LCQIANN/esp32s3-camera/enclosure/esp32s3-camera-shell-front.png

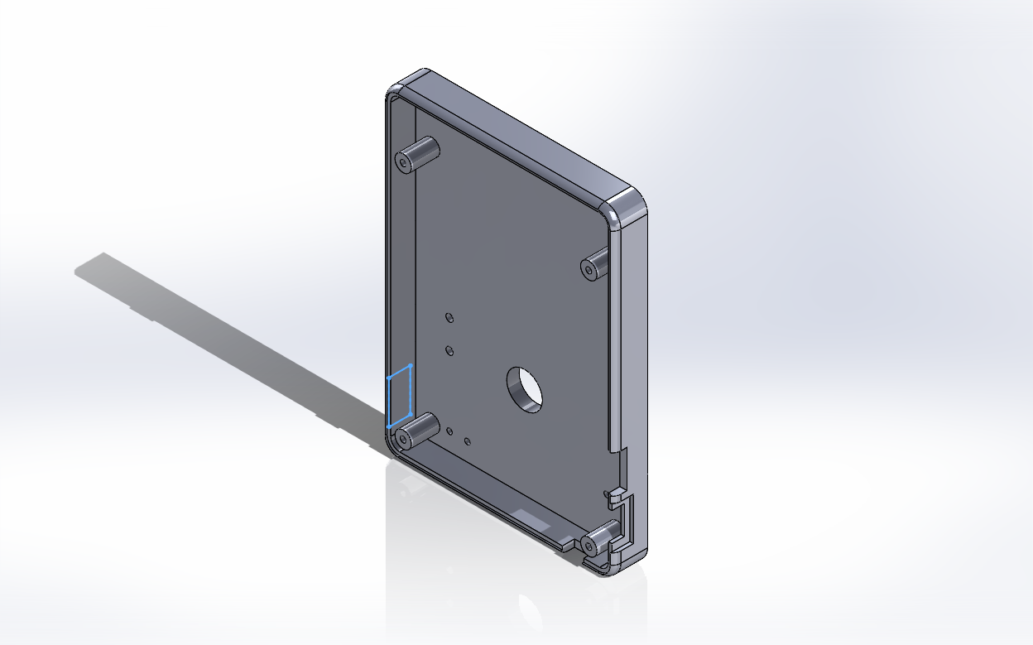
enclosure/esp32s3-camera-shell-front.png
