LCQIANN/esp32s3-camera/enclosure/esp32s3-camera-shutter-cap.png

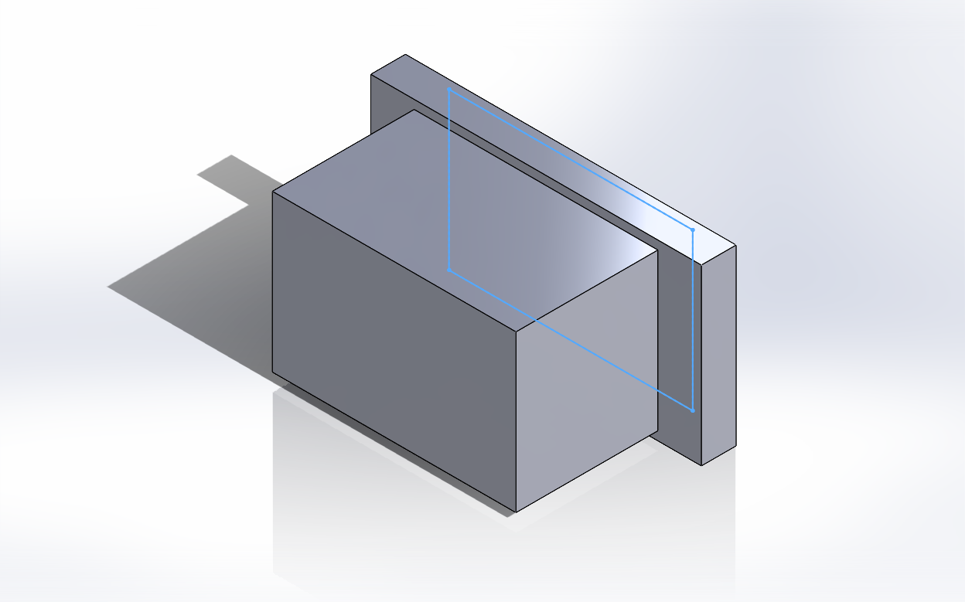
enclosure/esp32s3-camera-shutter-cap.png
