LCQIANN/esp32s3-camera/enclosure/fit-back-open-flat.png

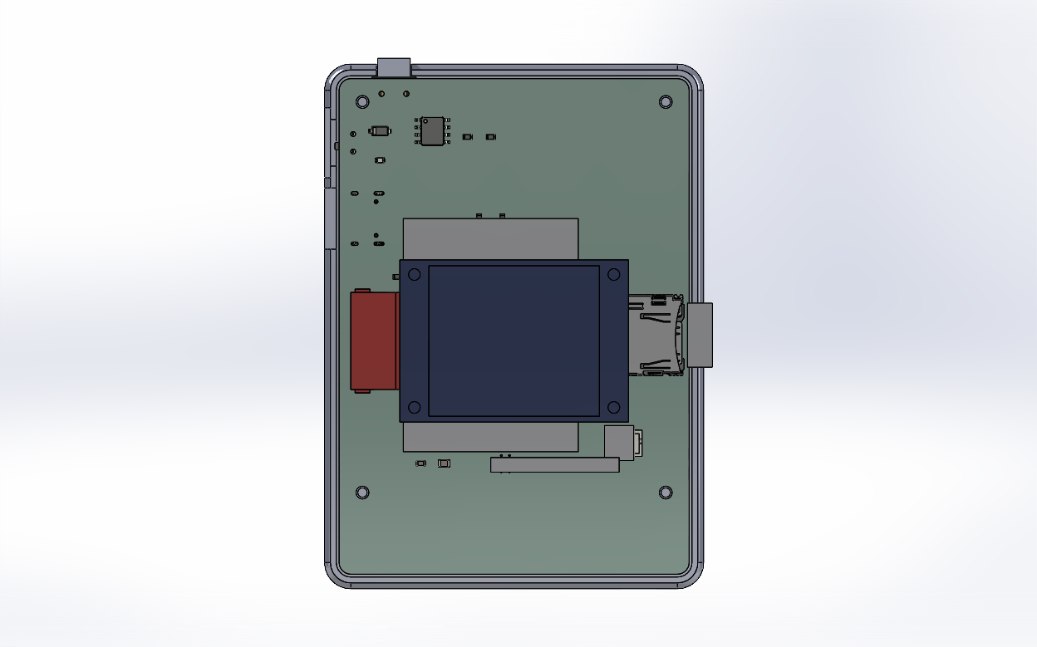
enclosure/fit-back-open-flat.png
