LCQIANN/esp32s3-camera/enclosure/fit-front-open-top.png

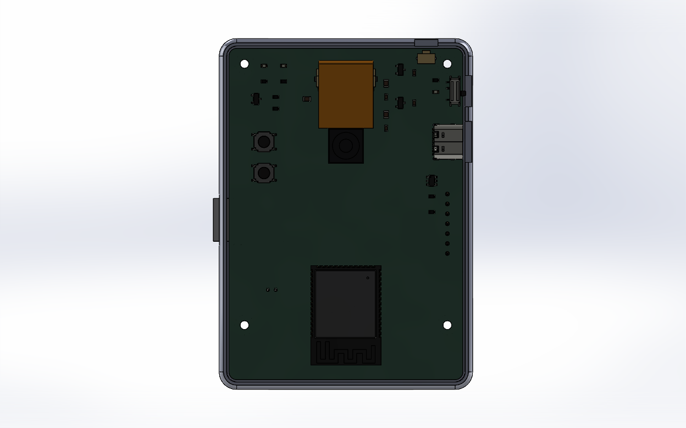
enclosure/fit-front-open-top.png
