LCQIANN/esp32s3-camera/enclosure/offboard-battery-card.png

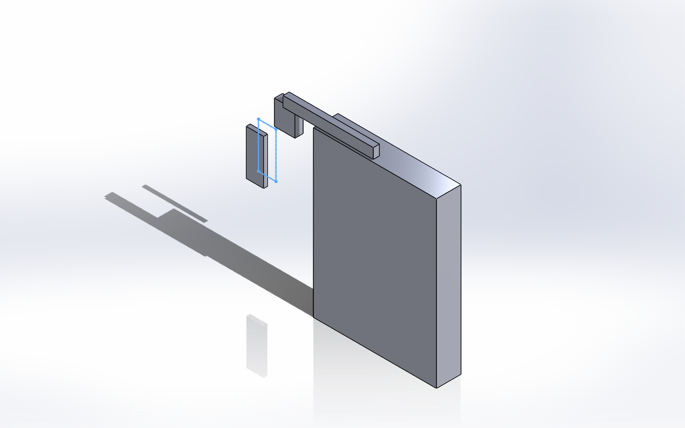
enclosure/offboard-battery-card.png
