LCQIANN/esp32s3-camera/enclosure/offboard-camera-module.png

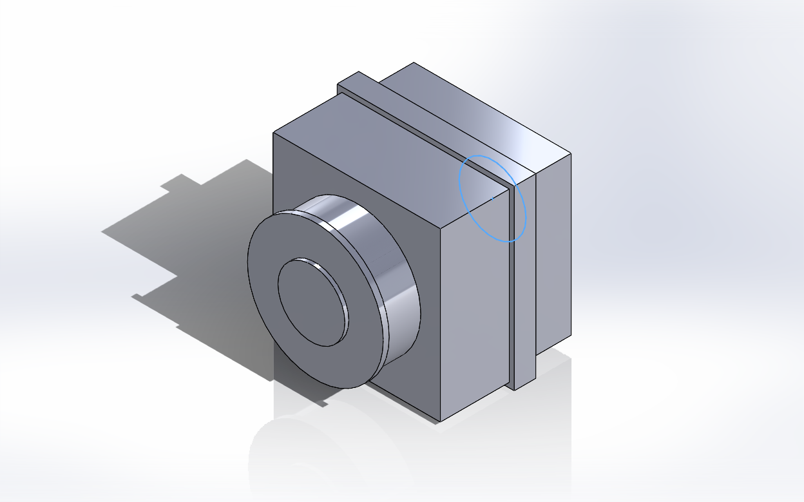
enclosure/offboard-camera-module.png
