LCQIANN/esp32s3-camera/enclosure/offboard-display-cable.png

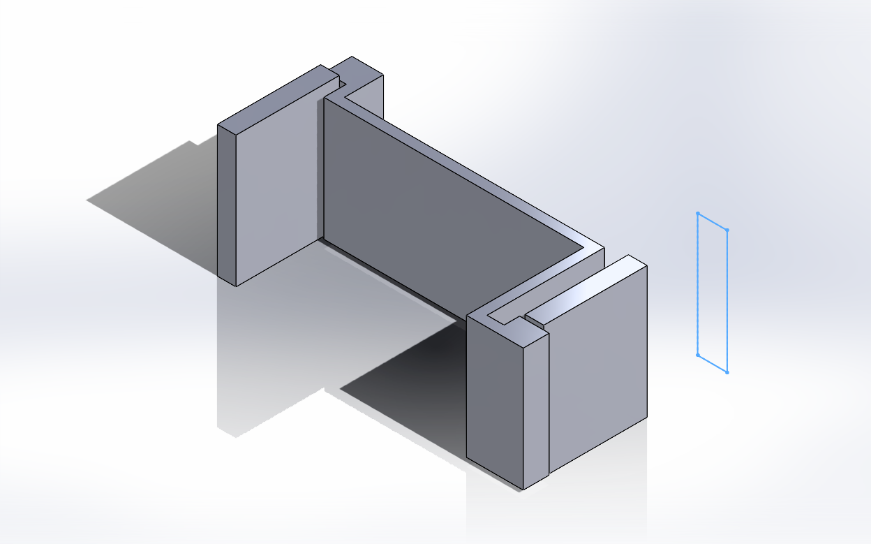
enclosure/offboard-display-cable.png
