LCQIANN/esp32s3-camera/enclosure/offboard-display-module.png

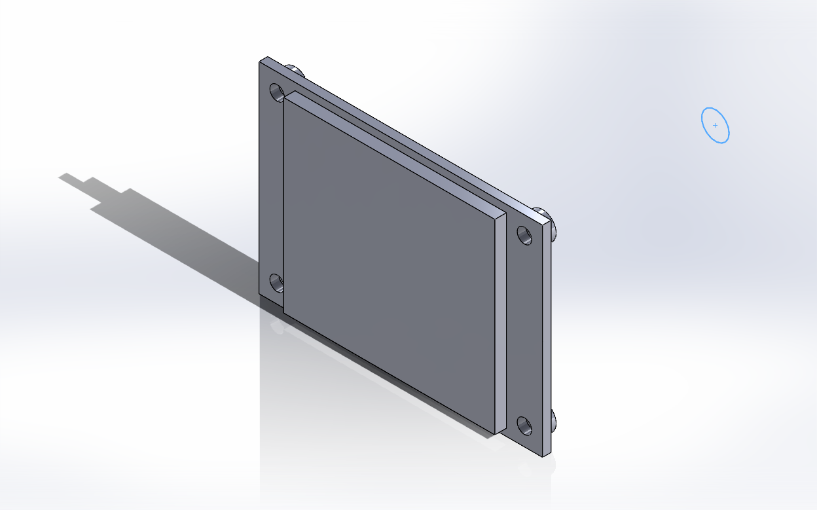
enclosure/offboard-display-module.png
