LCQIANN/esp32s3-camera/frames/s00.jpg

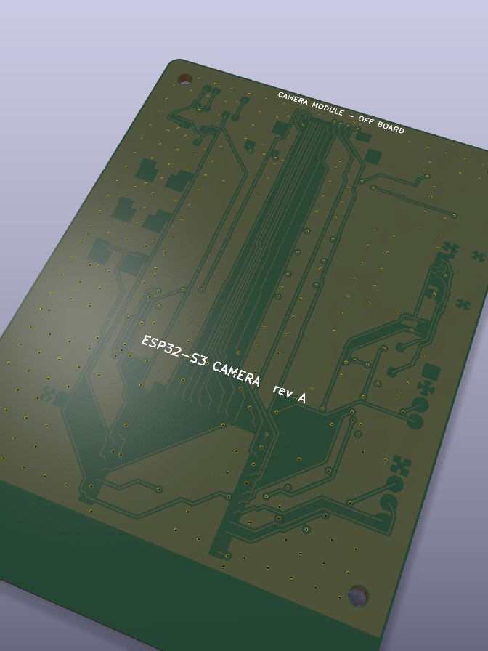
frames/s00.jpg
