LCQIANN/esp32s3-camera/frames/s01.jpg

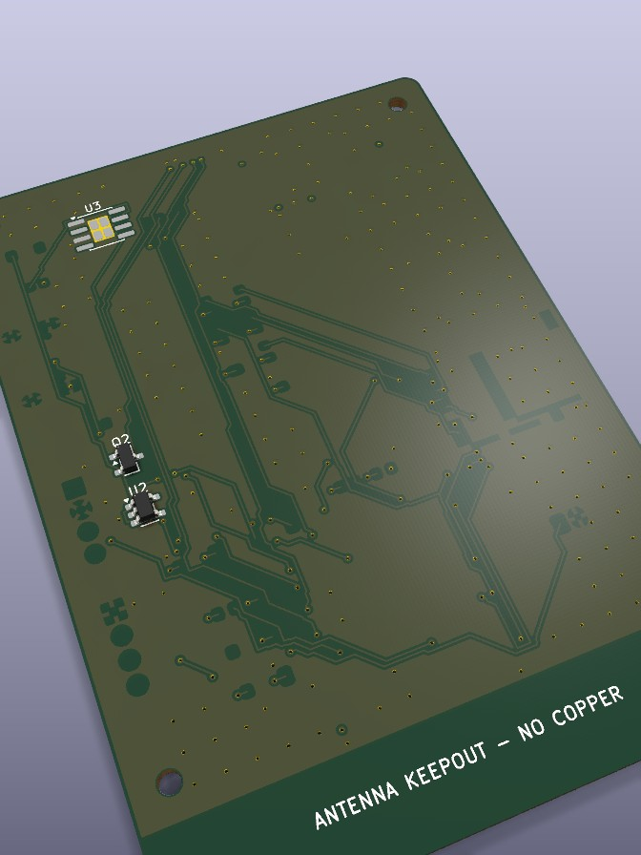
frames/s01.jpg
