LCQIANN/esp32s3-camera/frames/s03.jpg

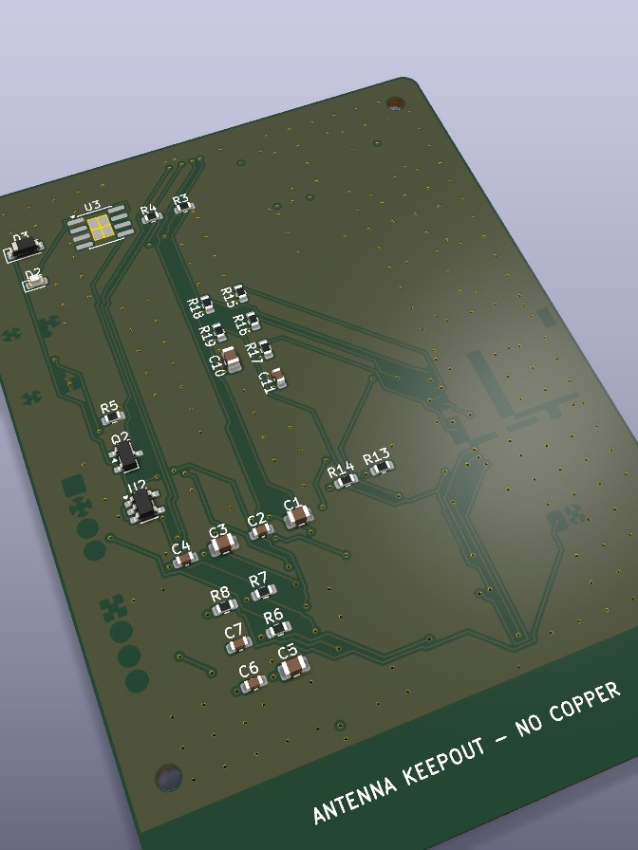
frames/s03.jpg
