LCQIANN/esp32s3-camera/frames/s07.jpg

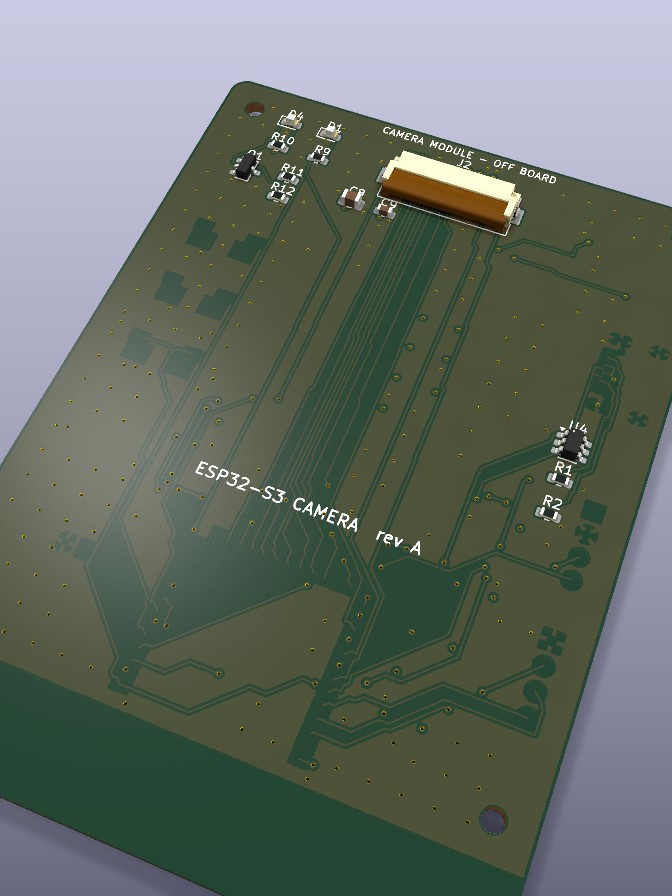
frames/s07.jpg
