LCQIANN/esp32s3-camera/frames/s09.jpg

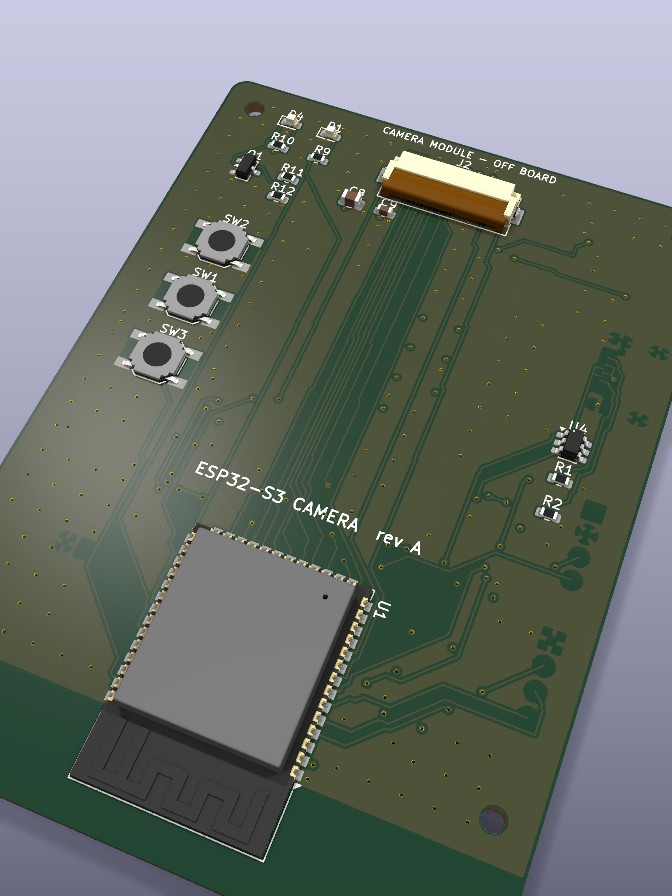
frames/s09.jpg
