LCQIANN/esp32s3-camera/frames/t00.jpg

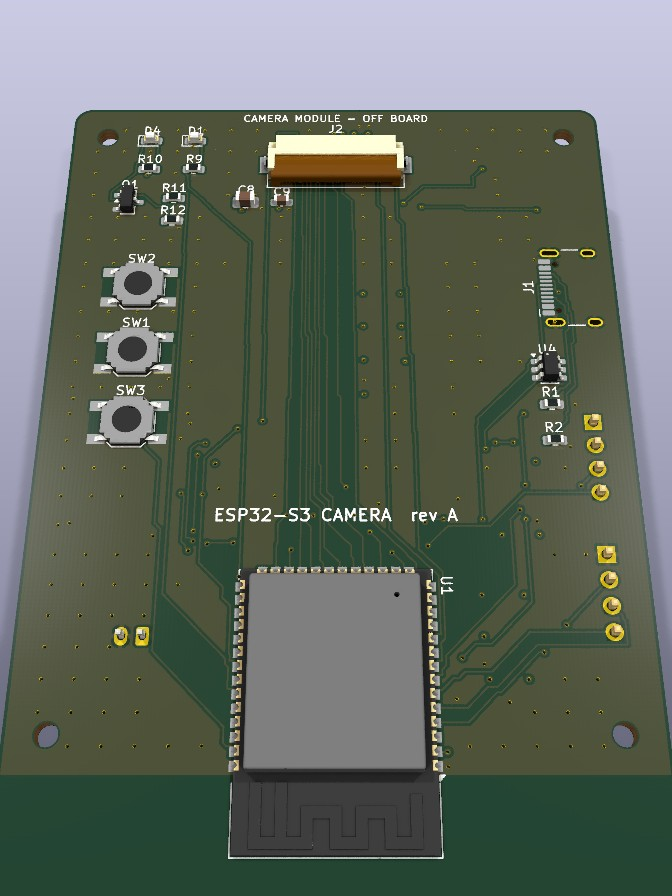
frames/t00.jpg
