LCQIANN/esp32s3-camera/frames/t01.jpg

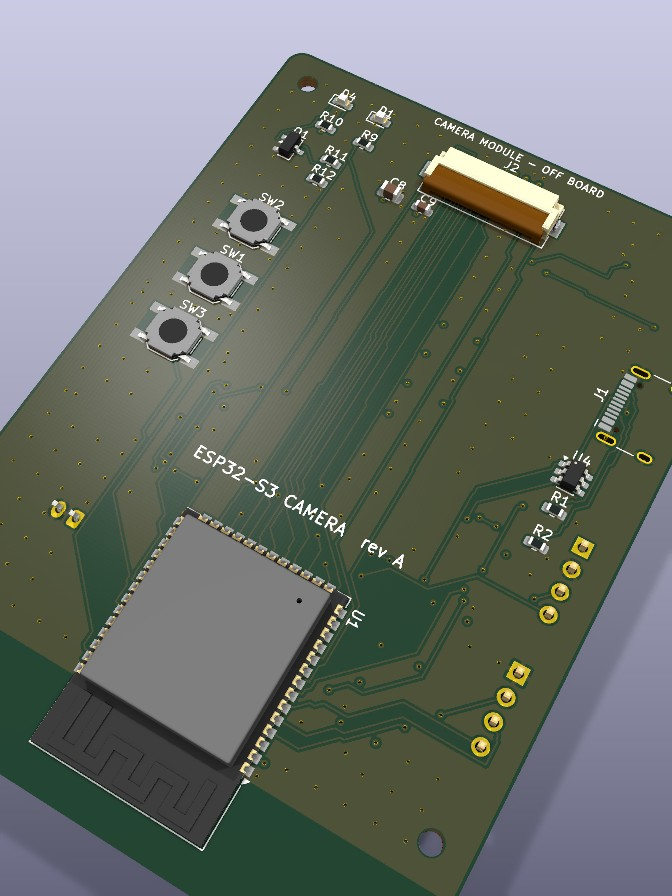
frames/t01.jpg
