LCQIANN/esp32s3-camera/frames/t02.jpg

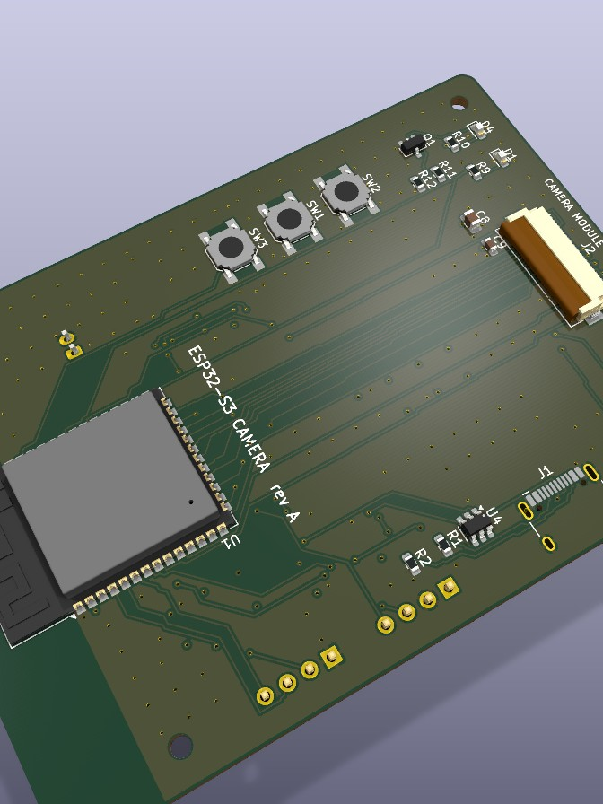
frames/t02.jpg
