LCQIANN/esp32s3-camera/frames/t03.jpg

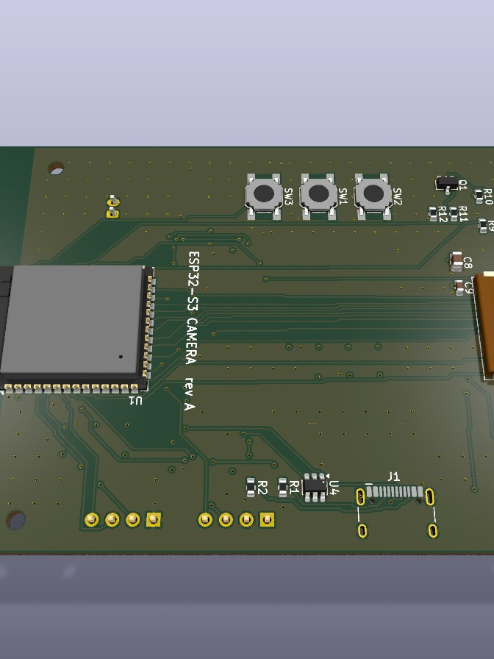
frames/t03.jpg
