LCQIANN/esp32s3-camera/frames/t04.jpg

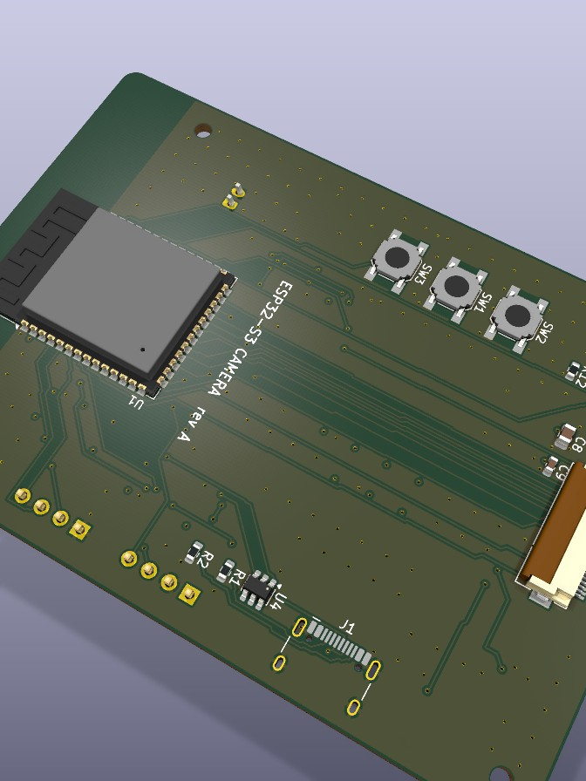
frames/t04.jpg
