LCQIANN/esp32s3-camera/frames/t05.jpg

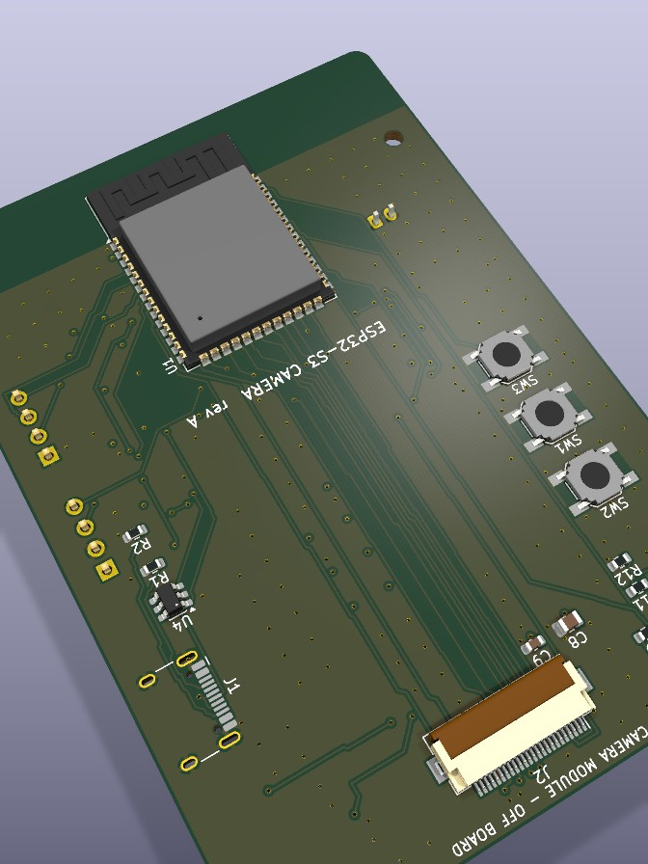
frames/t05.jpg
