LCQIANN/esp32s3-camera/frames/t06.jpg

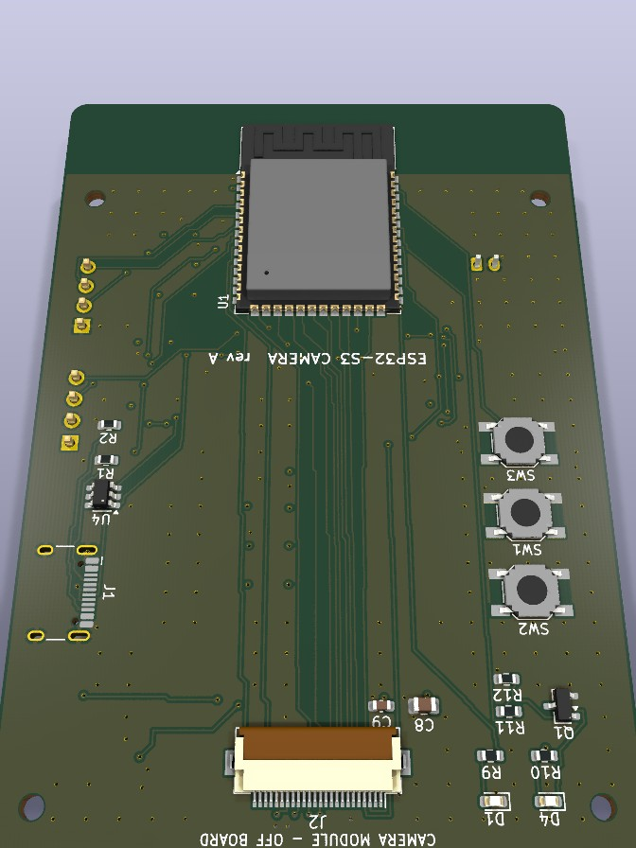
frames/t06.jpg
