LCQIANN/esp32s3-camera/frames/t07.jpg

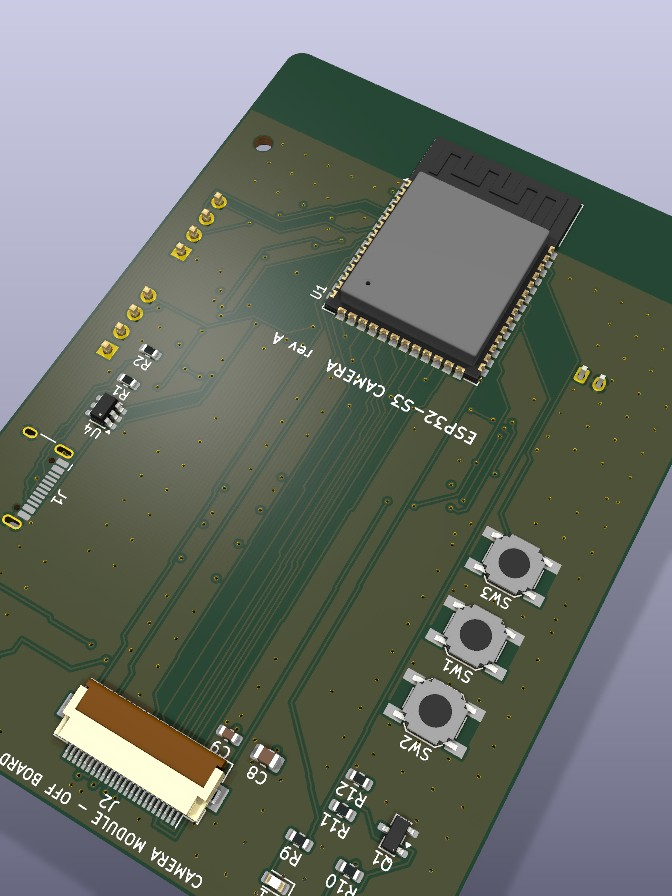
frames/t07.jpg
