LCQIANN/esp32s3-camera/frames/t08.jpg

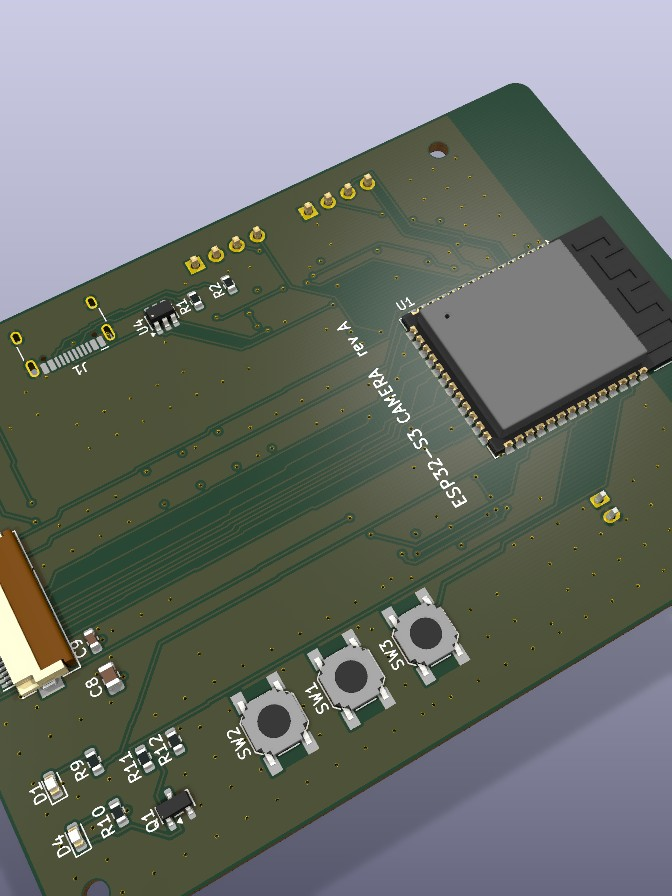
frames/t08.jpg
