LCQIANN/esp32s3-camera/frames/t09.jpg

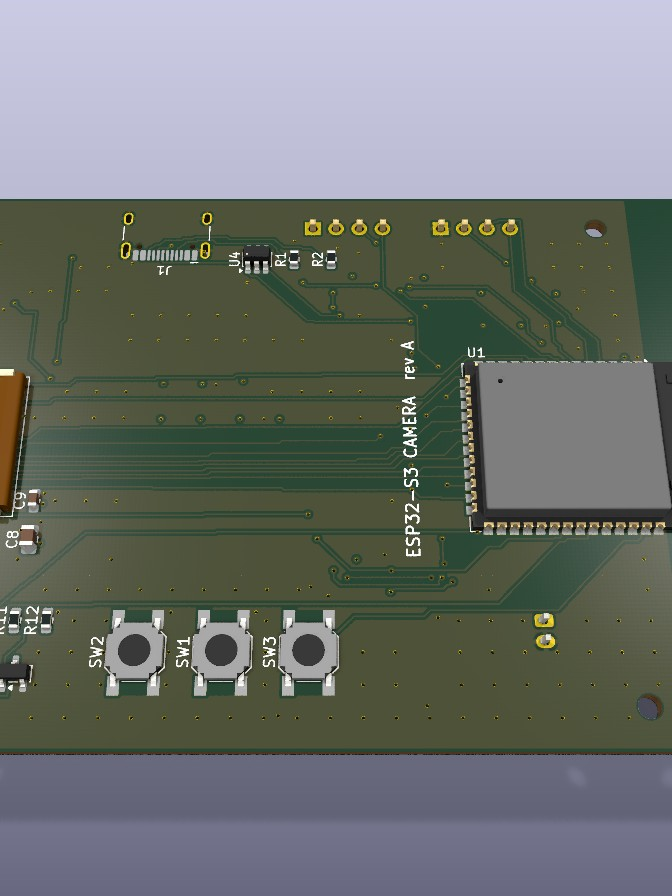
frames/t09.jpg
