LCQIANN/esp32s3-camera/frames/t10.jpg

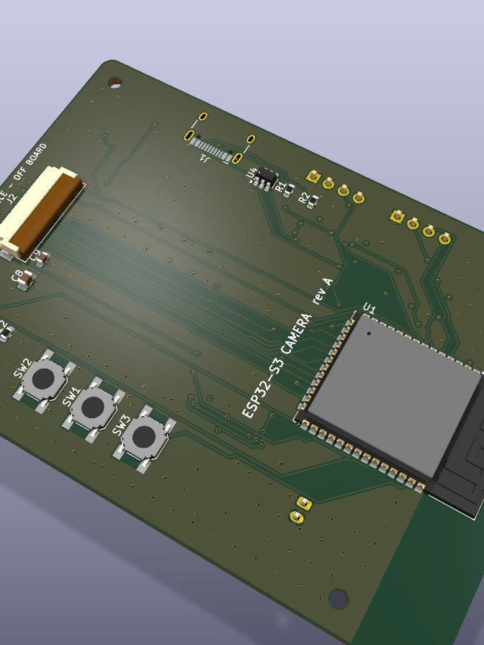
frames/t10.jpg
