LCQIANN/esp32s3-camera/frames/t11.jpg

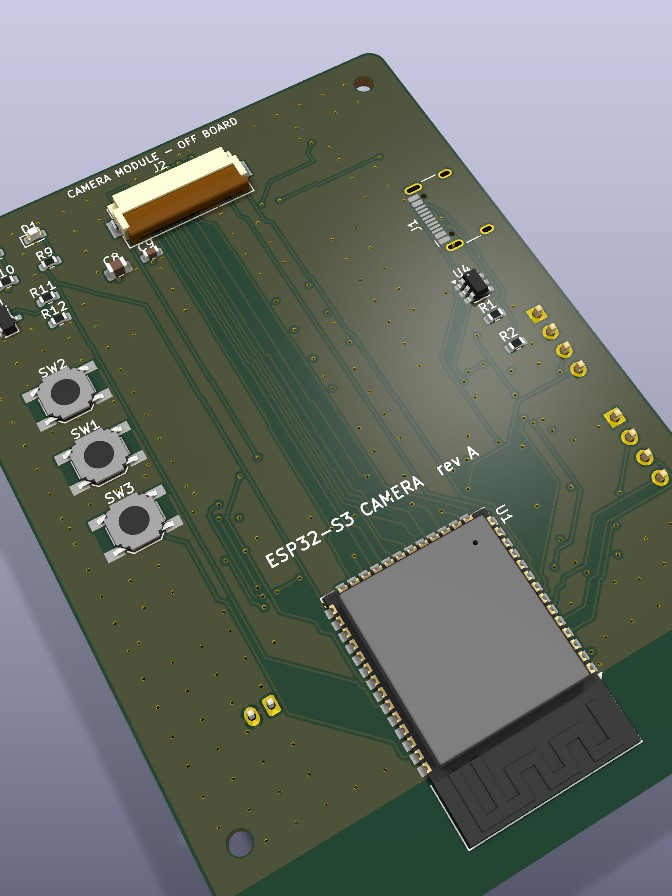
frames/t11.jpg
