LCQIANN/esp32s3-camera/render/assembled-iso-right.png

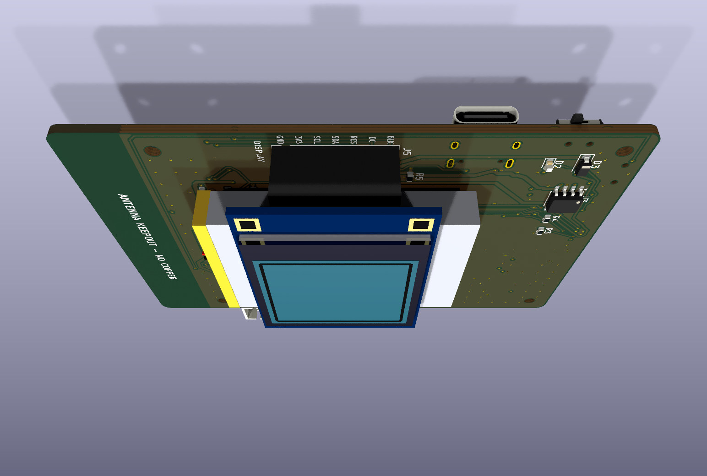
render/assembled-iso-right.png
