LCQIANN/esp32s3-camera/render/assembled-iso-top.png

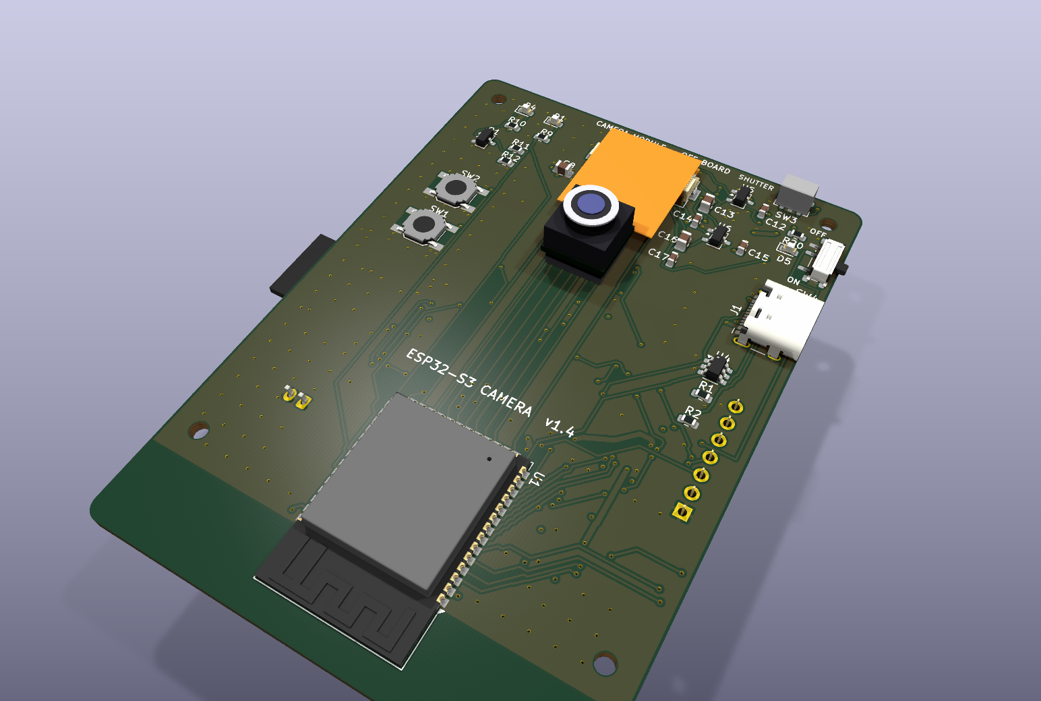
render/assembled-iso-top.png
